HorstBaerbel/LightBook/LightBook/data/pen.png

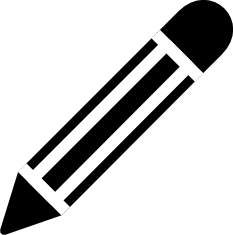
LightBook/data/pen.png
