HorstBaerbel/LightBook/LightBook/data/pick.png

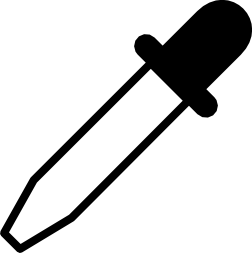
LightBook/data/pick.png
